Alan-JH/SimUFC/PCBs/Display layers updated/ufc_v4_scratchpad_layer3.step

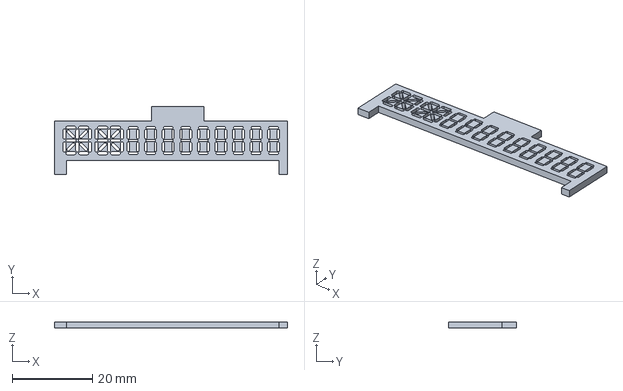
[picture p14: CAD file, 2021-05-30]
PCBs/Display layers updated/ufc_v4_scratchpad_layer3.step
58.0 x 16.8 x 1.60 mm
