Alan-JH/SimUFC/MCAD/STL Export/Key5.stl

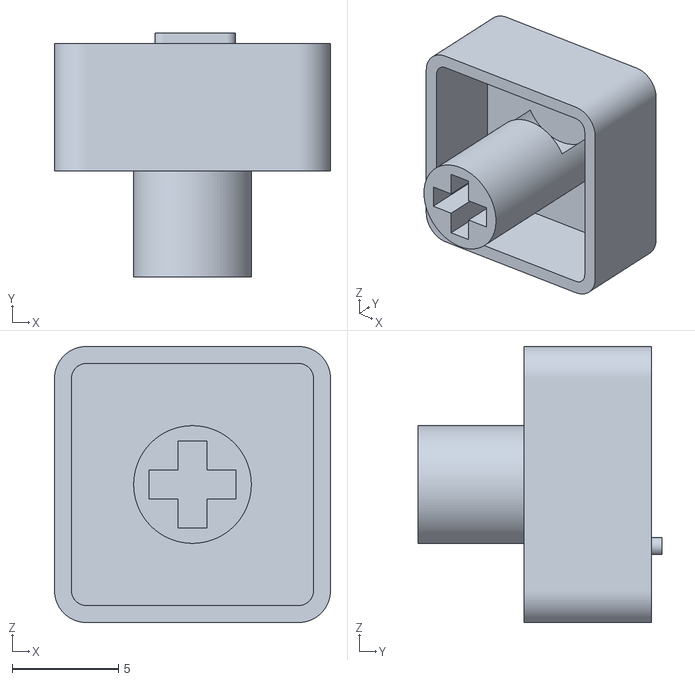
[picture p15: CAD file, 2021-07-18]
MCAD/STL Export/Key5.stl
13.0 x 11.5 x 13.0
