Alan-JH/SimUFC/PCBs/Display layers updated/ufc_v4_opt_layer4.step

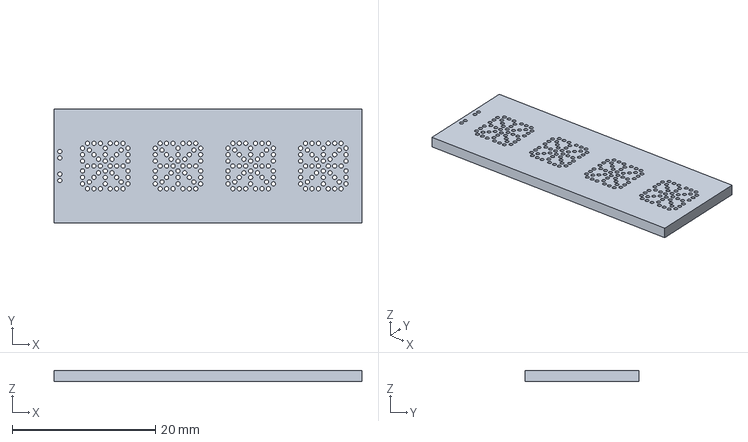
[picture p16: CAD file, 2021-05-30]
PCBs/Display layers updated/ufc_v4_opt_layer4.step
43.1 x 15.9 x 1.60 mm
