Alan-JH/SimUFC/MCAD/STL Export/L side.stl

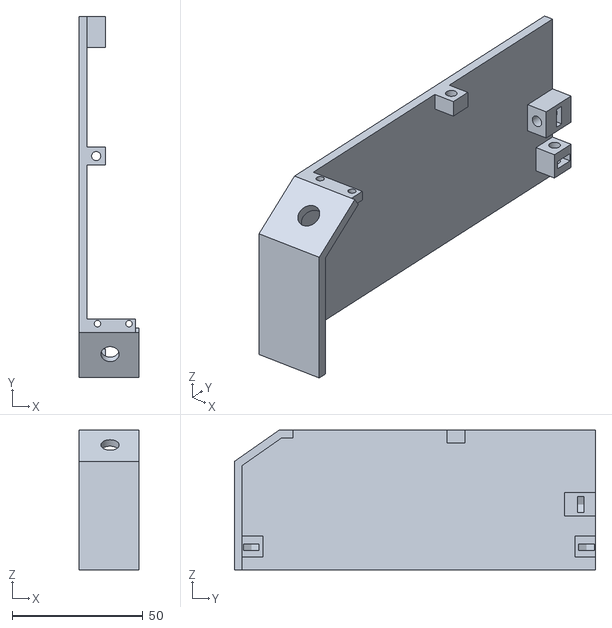
[picture p17: CAD file, 2021-07-18]
MCAD/STL Export/L side.stl
22.8 x 138.3 x 53.6
