Alan-JH/SimUFC/MCAD/STL Export/KeyRound.stl

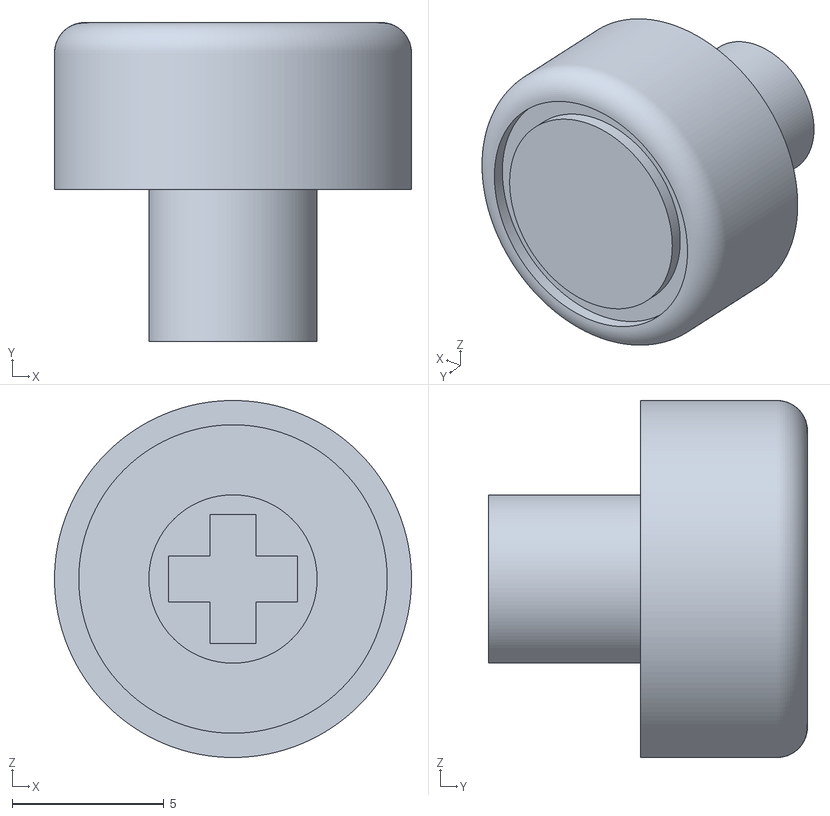
[picture p18: CAD file, 2021-07-18]
MCAD/STL Export/KeyRound.stl
11.8 x 10.5 x 11.8
