Alan-JH/SimUFC/MCAD/STL Export/Face spacer.stl

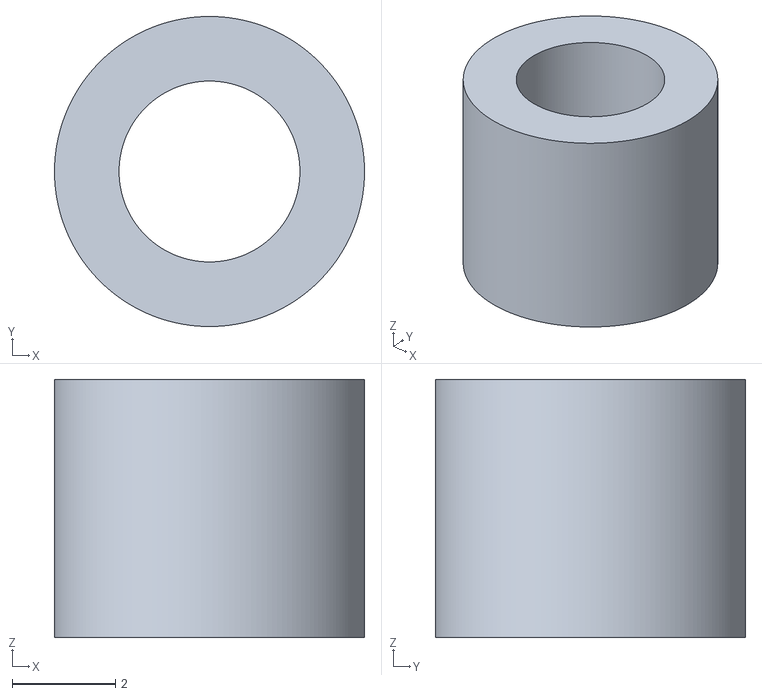
[picture p19: CAD file, 2021-06-10]
MCAD/STL Export/Face spacer.stl
6.00 x 6.00 x 5.00
