Alan-JH/SimUFC/MCAD/STL Export/Top.stl

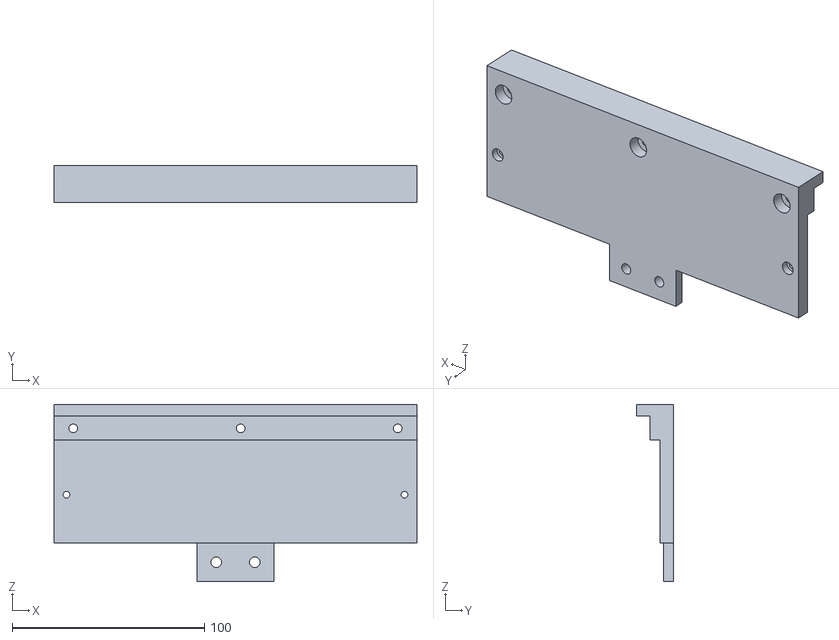
[picture p20: CAD file, 2021-06-10]
MCAD/STL Export/Top.stl
188.6 x 19.0 x 92.0
