Alan-JH/SimUFC/MCAD/STL Export/Face.stl

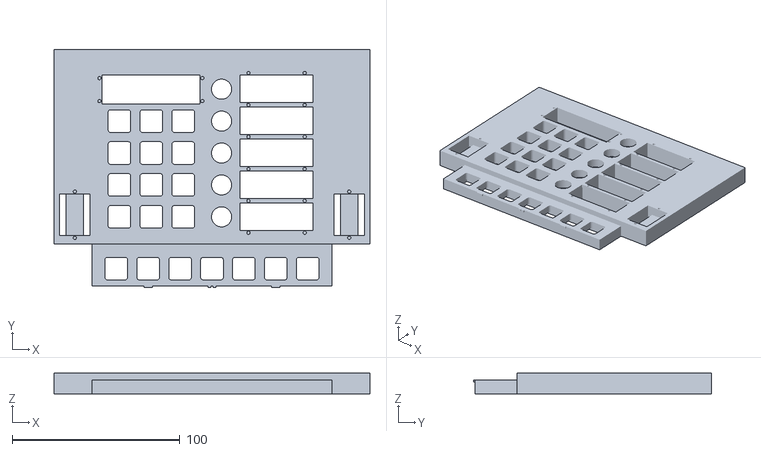
[picture p21: CAD file, 2021-06-10]
MCAD/STL Export/Face.stl
188.6 x 141.9 x 12.4
