Alan-JH/SimUFC/MCAD/STL Export/PCB spacer.stl

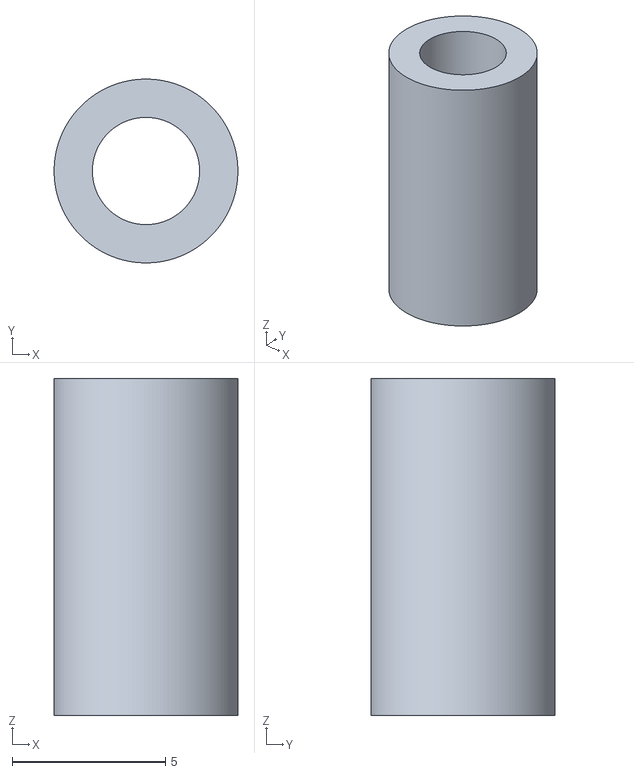
[picture p22: CAD file, 2021-06-08]
MCAD/STL Export/PCB spacer.stl
6.00 x 6.00 x 11.0
