Alan-JH/SimUFC/MCAD/STL Export/COMM retainer.stl

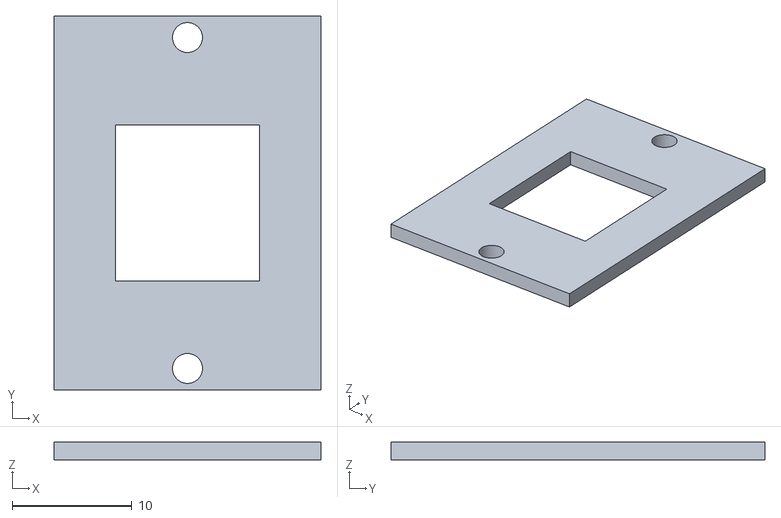
[picture p23: CAD file, 2021-06-08]
MCAD/STL Export/COMM retainer.stl
22.3 x 31.2 x 1.50
