Alan-JH/SimUFC/MCAD/STL Export/Keypadplate.stl

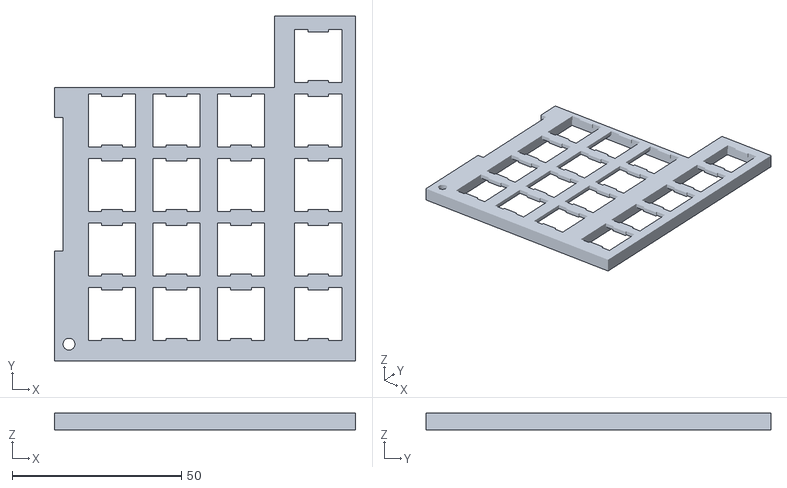
[picture p24: CAD file, 2021-06-08]
MCAD/STL Export/Keypadplate.stl
88.9 x 101.8 x 5.00
