Alan-JH/SimUFC/MCAD/STL Export/Lower bar switch plate.stl

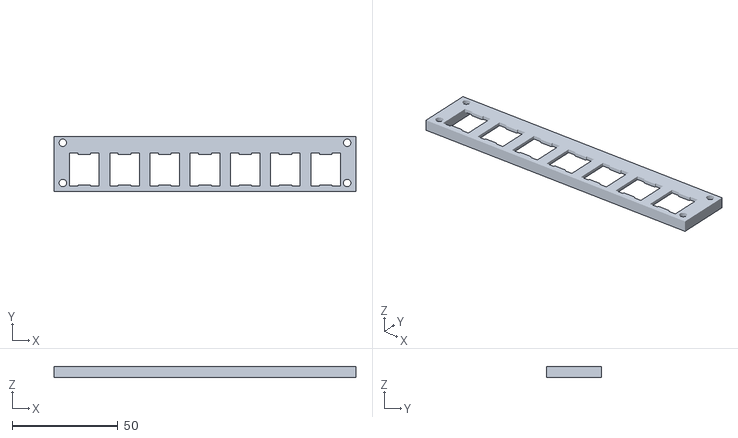
[picture p25: CAD file, 2021-06-08]
MCAD/STL Export/Lower bar switch plate.stl
143.0 x 26.1 x 5.00
