Alan-JH/SimUFC/MCAD/STL Export/Back.stl

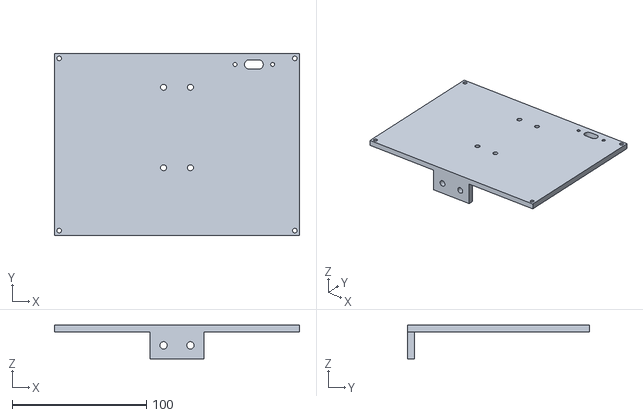
[picture p26: CAD file, 2021-06-08]
MCAD/STL Export/Back.stl
182.6 x 135.3 x 25.0
