Alan-JH/SimUFC/MCAD/STL Export/Scratchpad retainer.stl

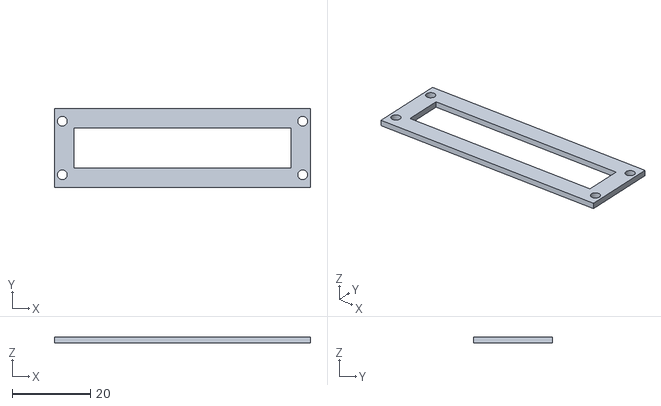
[picture p27: CAD file, 2021-06-08]
MCAD/STL Export/Scratchpad retainer.stl
65.4 x 20.3 x 1.50
