Alan-JH/SimUFC/MCAD/STL Export/OPT retainer.stl

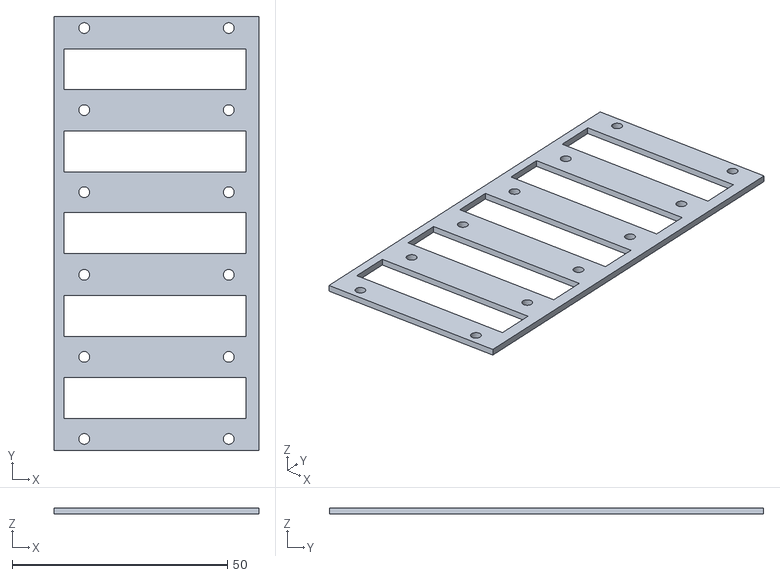
[picture p28: CAD file, 2021-06-08]
MCAD/STL Export/OPT retainer.stl
47.6 x 100.8 x 1.50
