Alan-JH/SimUFC/MCAD/STL Export/Lower bar spacer.stl

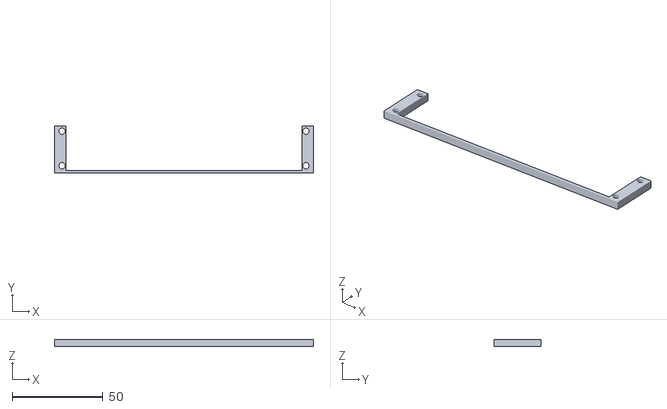
[picture p29: CAD file, 2021-06-08]
MCAD/STL Export/Lower bar spacer.stl
143.0 x 26.1 x 4.00
