Alan-JH/SimUFC/MCAD/STL Export/COMM.stl

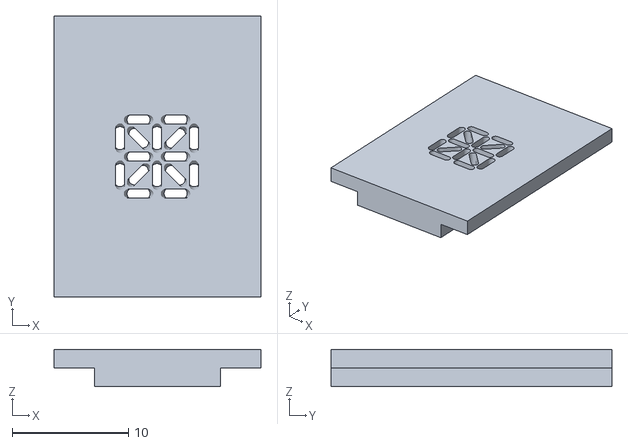
[picture p30: CAD file, 2021-06-08]
MCAD/STL Export/COMM.stl
17.8 x 24.1 x 3.20
