Alan-JH/SimUFC/PCBs/ufc_v4_opt.kicad_pcb

## KiCad design PCBs/ufc_v4_opt.kicad_pcb (2021-05-15)

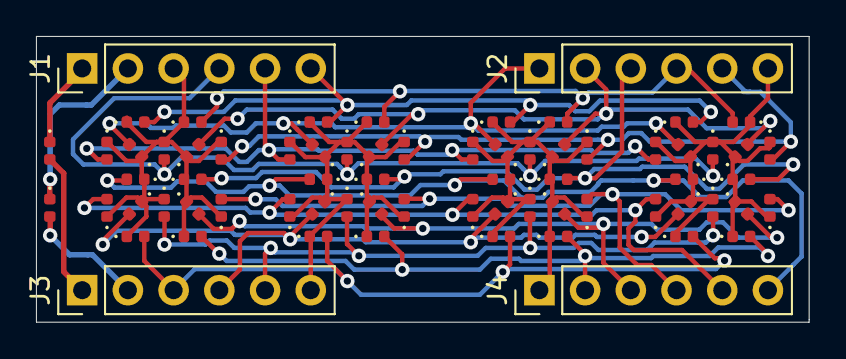
[picture p37: board ufc_v4_opt.kicad_pcb from above]

Board: 2 copper layers, 42.9 x 15.9 mm, 70 parts (0 on the bottom side), 24 nets.

Parts:
D1, D2, D3, D4, D5, D6, D7, D8, D9, D10, D11, D12, D13, D14, D15, D16, D17, D18, D19, D20, D21, D22, D23, D24, D25, D26, D27, D28, D29, D30, D31, D32, D33, D34, D35, D36, D37, D38, D39, D40, D41, D42, D43, D44, D45, D46, D47, D48, D49, D50, D51, D52, D53, D54, D55, D56, D57, D58, D59, D60, D61, D62, D63, D64, D65, D66: LED; LED_0402_1005Metric
J1, J2, J3, J4: Conn_01x06_Male; PinHeader_1x06_P2.54mm_Vertical

Connections:
/DIG0: D1.1, D2.1, D3.1, D4.1, D5.1, D6.1, D7.1, D8.1, D9.1, D10.1, D11.1, D12.1, D13.1, D14.1, D15.1, D16.1, J1.3
/DIG1: D17.1, D18.1, D19.1, D20.1, D21.1, D22.1, D23.1, D24.1, D25.1, D26.1, D27.1, D28.1, D29.1, D30.1, D31.1, D32.1, J3.6
/DIG2: D33.1, D34.1, D35.1, D36.1, D37.1, D38.1, D39.1, D40.1, D41.1, D42.1, D43.1, D44.1, D45.1, D46.1, D47.1, D48.1, J4.1
/DIG3: D49.1, D50.1, D51.1, D52.1, D53.1, D54.1, D55.1, D56.1, D57.1, D58.1, D59.1, D60.1, D61.1, D62.1, D63.1, D64.1, J2.6
/DOT1+: D65.2, J3.1
/DOT1-: D65.1, J1.1
/DOT2+: D66.2, J3.2
/DOT2-: D66.1, J1.2
/SEGA: D7.2, D23.2, D39.2, D55.2, J3.3
/SEGB: D8.2, D24.2, D40.2, D56.2, J1.4
/SEGC: D1.2, D17.2, D33.2, D49.2, J1.5
/SEGD: D3.2, D19.2, D35.2, D51.2, J1.6
/SEGDP: D2.2, D18.2, D34.2, D50.2, J4.5
/SEGE: D6.2, D22.2, D38.2, D54.2, J3.4
/SEGF: D5.2, D21.2, D37.2, D53.2, J4.6
/SEGG: D4.2, D20.2, D36.2, D52.2, J2.1
/SEGH: D9.2, D25.2, D41.2, D57.2, J3.5
/SEGJ: D14.2, D30.2, D46.2, D62.2, J4.2
/SEGK: D13.2, D29.2, D45.2, D61.2, J4.3
/SEGL: D12.2, D28.2, D44.2, D60.2, J2.3
/SEGM: D11.2, D27.2, D43.2, D59.2, J2.2
/SEGN: D10.2, D26.2, D42.2, D58.2, J2.4
/SEGP: D16.2, D32.2, D48.2, D64.2, J4.4
/SEGQ: D15.2, D31.2, D47.2, D63.2, J2.5
