Alan-JH/SimUFC/PCBs/ufc_v4_comm.kicad_pcb

## KiCad design PCBs/ufc_v4_comm.kicad_pcb (2021-05-15)

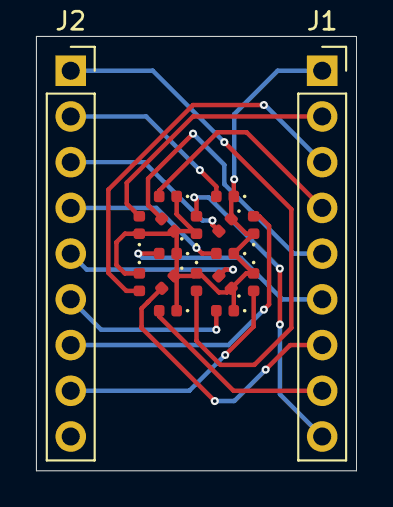
[picture p38: board ufc_v4_comm.kicad_pcb from above]

Board: 2 copper layers, 17.8 x 24.1 mm, 18 parts (0 on the bottom side), 17 nets.

Parts:
D1, D2, D3, D4, D5, D6, D7, D8, D9, D10, D11, D12, D13, D14, D15, D16: LED; LED_0402_1005Metric
J1, J2: Conn_01x09_Male; PinSocket_1x09_P2.54mm_Vertical

Connections:
/COM: D1.1, D2.1, D3.1, D4.1, D5.1, D6.1, D7.1, D8.1, D9.1, D10.1, D11.1, D12.1, D13.1, D14.1, D15.1, D16.1, J1.1
/SEGA: D1.2, J1.2
/SEGB: D2.2, J1.3
/SEGC: D3.2, J1.4
/SEGD: D4.2, J1.5
/SEGDP: D16.2, J2.8
/SEGE: D5.2, J1.6
/SEGF: D6.2, J1.7
/SEGG: D7.2, J1.8
/SEGH: D8.2, J1.9
/SEGJ: D9.2, J2.1
/SEGK: D10.2, J2.2
/SEGL: D11.2, J2.3
/SEGM: D12.2, J2.4
/SEGN: D13.2, J2.5
/SEGP: D14.2, J2.6
/SEGQ: D15.2, J2.7
