Alan-JH/SimUFC/Firmware/UFC_Firmware/CharacterMap.h

//Includes all ascii characters that can be displayed on a 16 segment display, not just those that appear in the hornet UFC, for the sake of future proofing
//Most character patterns are adapted from https://github.com/dmadison/LED-Segment-ASCII
//Two digit numbers also included for those that appear on the COMM displays and Scratchpad digits 1-2

#define lenChars 106
String characters[lenChars] = {
  " ",
  "!",
  "#",
  "$",
  "%",
  "&",
  "'",
  "(",
  ")",
  "*",
  "+",
  ",",
  "-",
  ".",
  "/",
  "0",
  "1",
  "2",
  "3",
  "4",
  "5",
  "6",
  "7",
  "8",
  "9",
  ":",
  ";",
  "<",
  "=",
  ">",
  "?",
  "@",
  "A",
  "B",
  "C",
  "D",
  "E",
  "F",
  "G",
  "H",
  "I",
  "J",
  "K",
  "L",
  "M",
  "N",
  "O",
  "P",
  "Q",
  "R",
  "S",
  "T",
  "U",
  "V",
  "W",
  "X",
  "Y",
  "Z",
  "[",
  "\\",
  "]",
  "^",
  "_",
  "`",
  "a",
  "b",
  "c",
  "d",
  "e",
  "f",
  "g",
  "h",
  "i",
  "j",
  "k",
  "l",
  "m",
  "n",
  "o",
  "p",
  "q",
  "r",
  "s",
  "t",
  "u",
  "v",
  "w",
  "x",
  "y",
  "z",
  "{",
  "|",
  "}",
  "~",
  "10", //Specifically for the Hornet UFC's Scratchpad + COMM:
  "11",
  "12",
  "13",
  "14",
  "15",
  "16",
  "17",
  "18",
  "19",
  "20", 
  //Specifically because DCS BIOS is weird:
  "--"
};

/* 7 Seg: A, B, C, D, E, F, G
   index: 0, 1, 2, 3, 4, 5, 6
   --A--
  |     |
  |     |
  F     B
  |     |
  |     |
   --G--
  |     |
  |     |
  E     C
  |     |
  |     |
   --D--

 */

 uint8_t Map7[94][7] = {
  {0, 0, 0, 0, 0, 0, 0},
  {0, 1, 1, 0, 0, 0, 0},
  {0, 1, 1, 1, 1, 1, 1},
  {1, 0, 1, 1, 0, 1, 1},
  {0, 1, 0, 0, 1, 0, 1},
  {0, 1, 1, 0, 0, 0, 1},
  {0, 0, 0, 0, 0, 1, 0},
  {1, 0, 0, 1, 0, 1, 0},
  {1, 1, 0, 1, 0, 0, 0},
  {1, 0, 0, 0, 0, 1, 0},
  {0, 0, 0, 0, 1, 1, 1},
  {0, 0, 0, 0, 1, 0, 0},
  {0, 0, 0, 0, 0, 0, 1},
  {0, 0, 1, 1, 1, 0, 1},
  {0, 1, 0, 0, 1, 0, 1},
  {1, 1, 1, 1, 1, 1, 0},
  {0, 1, 1, 0, 0, 0, 0},
  {1, 1, 0, 1, 1, 0, 1},
  {1, 1, 1, 1, 0, 0, 1},
  {0, 1, 1, 0, 0, 1, 1},
  {1, 0, 1, 1, 0, 1, 1},
  {0, 0, 1, 1, 1, 1, 1},
  {1, 1, 1, 0, 0, 0, 0},
  {1, 1, 1, 1, 1, 1, 1},
  {1, 1, 1, 0, 0, 1, 1},
  {1, 0, 0, 1, 0, 0, 0},
  {1, 0, 1, 1, 0, 0, 0},
  {1, 0, 0, 0, 0, 1, 1},
  {0, 0, 0, 1, 0, 0, 1},
  {1, 1, 0, 0, 0, 0, 1},
  {1, 1, 0, 0, 1, 0, 1},
  {1, 1, 0, 0, 0, 1, 1},
  {1, 1, 1, 0, 1, 1, 1},
  {0, 0, 1, 1, 1, 1, 1},
  {1, 0, 0, 1, 1, 1, 0},
  {0, 1, 1, 1, 1, 0, 1},
  {1, 0, 0, 1, 1, 1, 1},
  {1, 0, 0, 0, 1, 1, 1},
  {1, 0, 1, 1, 1, 1, 0},
  {0, 1, 1, 0, 1, 1, 1},
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
 };

/*16 Seg: A, B, C, D, E, F, G, H, I, J, K, L, M, N, O, P
 *index:  0, 1, 2, 3, 4, 5, 6, 7, 8, 9,10,11,12,13,14,15
   --A-- --B--
  |\    |    /|
  | \   |   / |
  H  I  J  K  C
  |   \ | /   |
  |    \|/    |
   --P-- --L--
  |    /|\    |
  |   / | \   |
  G  O  N  M  D
  | /   |   \ |
  |/    |    \|
   --F-- --E--
*/
uint8_t Map16[106][16] = {
 //A, B, C, D, E, F, G, H, I, J, K, L, M, N, O, P
  {0, 0, 0, 0, 0, 0, 0, 0, 0, 0, 0, 0, 0, 0, 0, 0},
  {0, 0, 1, 1, 0, 0, 0, 0, 0, 0, 0, 0, 0, 0, 0, 0},
  {0, 0, 1, 1, 1, 1, 0, 0, 0, 1, 0, 1, 0, 1, 0, 1},
  {1, 1, 0, 1, 1, 1, 0, 1, 0, 1, 0, 1, 0, 1, 0, 1},
  {1, 0, 0, 1, 1, 0, 0, 1, 0, 1, 1, 1, 0, 1, 1, 1},
  {1, 0, 0, 0, 1, 1, 1, 0, 1, 1, 0, 0, 1, 0, 0, 1},
  {0, 0, 0, 0, 0, 0, 0, 0, 0, 1, 0, 0, 0, 0, 0, 0},
  {0, 0, 0, 0, 0, 0, 0, 0, 0, 0, 1, 0, 1, 0, 0, 0},
  {0, 0, 0, 0, 0, 0, 0, 0, 1, 0, 0, 0, 0, 0, 1, 0},
  {0, 0, 0, 0, 0, 0, 0, 0, 1, 1, 1, 1, 1, 1, 1, 1},
  {0, 0, 0, 0, 0, 0, 0, 0, 0, 1, 0, 1, 0, 1, 0, 1},
  {0, 0, 0, 0, 0, 0, 0, 0, 0, 0, 0, 0, 0, 0, 1, 0},
  {0, 0, 0, 0, 0, 0, 0, 0, 0, 0, 0, 1, 0, 0, 0, 1},
  {0, 0, 0, 1, 1, 0, 0, 0, 0, 0, 0, 1, 0, 1, 0, 0},
  {0, 0, 0, 0, 0, 0, 0, 0, 0, 0, 1, 0, 0, 0, 1, 0},
  {0, 1, 1, 1, 1, 0, 0, 0, 0, 1, 0, 0, 0, 1, 0, 0}, //0
  {0, 0, 1, 1, 0, 0, 0, 0, 0, 0, 0, 0, 0, 0, 0, 0}, //1
  {0, 1, 1, 0, 1, 0, 0, 0, 0, 0, 0, 1, 0, 1, 0, 0}, //2
  {0, 1, 1, 1, 1, 0, 0, 0, 0, 0, 0, 1, 0, 0, 0, 0}, //3
  {0, 0, 1, 1, 0, 0, 0, 0, 0, 1, 0, 1, 0, 0, 0, 0}, //4
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
  {0, 1, 1, 1, 0, 0, 1, 1, 0, 0, 0, 0, 0, 0, 0, 0},
  {0, 1, 1, 1, 1, 0, 1, 1, 0, 1, 0, 1, 0, 1, 0, 0},
  {0, 1, 1, 1, 0, 0, 1, 1, 0, 1, 0, 1, 0, 0, 0, 0},
  {1, 1, 1, 1, 1, 1, 1, 0, 0, 1, 0, 0, 0, 1, 0, 1},
  {0, 0, 0, 0, 0, 0, 0, 0, 0, 0, 0, 1, 0, 0, 0, 1} //--
};
