Alan-JH/SimUFC/Firmware/UFC_Firmware/SegmentMap.h

/*16 Seg: A, B, C, D, E, F, G, H, I, J, K, L, M, N, O, P
 *index:  0, 1, 2, 3, 4, 5, 6, 7, 8, 9,10,11,12,13,14,15
   --A-- --B--
  |\    |    /|
  | \   |   / |
  H  I  J  K  C
  |   \ | /   |
  |    \|/    |
   --P-- --L--
  |    /|\    |
  |   / | \   |
  G  O  N  M  D
  | /   |   \ |
  |/    |    \|
   --F-- --E--

7 Seg: A, B, C, D, E, F, G
index: 0, 1, 2, 3, 4, 5, 6
   --A--
  |     |
  |     |
  F     B
  |     |
  |     |
   --G--
  |     |
  |     |
  E     C
  |     |
  |     |
   --D--

*/

//Scratchpad digits 1 and 2
uint8_t ScratchPad16[2][16][2] = {
  {{8, 6}, {9, 7}, {9, 2}, {9,1}, {9, 3}, {8, 2}, {8, 7}, {16, 0}, {8, 5}, {8, 1}, {9, 6}, {9, 5}, {9, 4}, {17, 0}, {8, 3}, {8, 4}},
  {{10, 6}, {11, 7}, {11, 2}, {11, 1}, {11, 3}, {10, 2}, {10, 7}, {18, 0}, {10, 5}, {10, 1}, {11, 6}, {11, 5}, {11, 4}, {19, 0}, {10, 3}, {10, 4}}
};

//Scratchpad digits 3-11
uint8_t ScratchPad7[9][7][2] = {
  {{20, 0}, {12, 7}, {12, 6}, {12, 5}, {12, 4}, {12, 3}, {12, 2}},
  {{21, 0}, {13, 7}, {13, 6}, {13, 5}, {13, 4}, {13, 3}, {13, 2}},
  {{22, 0}, {14, 7}, {14, 6}, {14, 5}, {14, 4}, {14, 3}, {14, 2}},
  {{23, 0}, {15, 7}, {15, 6}, {15, 5}, {15, 4}, {15, 3}, {15, 2}},
  {{12, 1}, {12, 0}, {4, 7}, {4, 6}, {4, 5}, {4, 4}, {4, 3}},
  {{13, 1}, {13, 0}, {5, 7}, {5, 6}, {5, 5}, {5, 4}, {5, 3}},
  {{14, 1}, {14, 0}, {6, 7}, {6, 6}, {6, 5}, {6, 4}, {6, 3}},
  {{15, 1}, {15, 0}, {7, 7}, {7, 6}, {7, 5}, {7, 4}, {7, 3}},
  {{8, 9}, {8, 8}, {0, 15}, {0, 14}, {0, 13}, {0, 12}, {0, 11}}
};

//OPT1 DOT
uint8_t OPT1Dot[1][1][2] = {
  {{1, 8}}
};

//OPT1 digits 1-4
uint8_t OPT1Disp[4][16][2] = {
  {{9, 13}, {1, 12}, {1, 10}, {1, 11}, {9, 8}, {17, 8}, {1, 9}, {9, 14}, {9, 10}, {9, 15}, {1, 13}, {1, 14}, {1, 15}, {9, 9}, {9, 12}, {9, 11}},
  {{10, 13}, {2, 12}, {2, 10}, {2, 11}, {10, 8}, {18, 8}, {2, 9}, {10, 14}, {10, 10}, {10, 15}, {2, 13}, {2, 14}, {2, 15}, {10, 9}, {10, 12}, {10, 11}},
  {{11, 13}, {3, 12}, {3, 10}, {3, 11}, {11, 8}, {19, 8}, {3, 9}, {11, 14}, {11, 10}, {11, 15}, {3, 13}, {3, 14}, {3, 15}, {11, 9}, {11, 12}, {11, 11}},
  {{12, 13}, {4, 12}, {4, 10}, {4, 11}, {12, 8}, {20, 8}, {4, 9}, {12, 14}, {12, 10}, {12, 15}, {4, 13}, {4, 14}, {4, 15}, {12, 9}, {12, 12}, {12, 11}}
};

//OPT2 DOT
uint8_t OPT2Dot[1][1][2] = {
  {{40, 0}}
};

//OPT2 digits 1-4
uint8_t OPT2Disp[4][16][2] = {
  {{24, 3}, {32, 4}, {32, 6}, {32, 5}, {32, 0}, {24, 0}, {32, 7}, {24, 2}, {24, 6}, {24, 1}, {32, 3}, {32, 2}, {32, 1}, {24, 7}, {24, 4}, {24, 5}},
  {{25, 3}, {33, 4}, {33, 6}, {33, 5}, {33, 0}, {25, 0}, {33, 7}, {25, 2}, {25, 6}, {25, 1}, {33, 3}, {33, 2}, {33, 1}, {25, 7}, {25, 4}, {25, 5}},
  {{26, 3}, {34, 4}, {34, 6}, {34, 5}, {34, 0}, {26, 0}, {34, 7}, {26, 2}, {26, 6}, {26, 1}, {34, 3}, {34, 2}, {34, 1}, {26, 7}, {26, 4}, {26, 5}},
  {{27, 3}, {35, 4}, {35, 6}, {35, 5}, {35, 0}, {27, 0}, {35, 7}, {27, 2}, {27, 6}, {27, 1}, {35, 3}, {35, 2}, {35, 1}, {27, 7}, {27, 4}, {27, 5}}
};

//OPT3 DOT
uint8_t OPT3Dot[1][1][2] = {
  {{44, 0}}
};

//OPT3 digits 1-4
uint8_t OPT3Disp[4][16][2] = {
  {{28, 3}, {36, 4}, {36, 6}, {36, 5}, {36, 0}, {28, 0}, {36, 7}, {28, 2}, {28, 6}, {28, 1}, {36, 3}, {36, 2}, {36, 1}, {28, 7}, {28, 4}, {28, 5}},
  {{29, 3}, {37, 4}, {37, 6}, {37, 5}, {37, 0}, {29, 0}, {37, 7}, {29, 2}, {29, 6}, {29, 1}, {37, 3}, {37, 2}, {37, 1}, {29, 7}, {29, 4}, {29, 5}},
  {{30, 3}, {38, 4}, {38, 6}, {38, 5}, {38, 0}, {30, 0}, {38, 7}, {30, 2}, {30, 6}, {30, 1}, {38, 3}, {38, 2}, {38, 1}, {30, 7}, {30, 4}, {30, 5}},
  {{31, 3}, {39, 4}, {39, 6}, {39, 5}, {39, 0}, {31, 0}, {39, 7}, {31, 2}, {31, 6}, {31, 1}, {39, 3}, {39, 2}, {39, 1}, {31, 7}, {31, 4}, {31, 5}}
};

//OPT 4 DOT
uint8_t OPT4Dot[1][1][2] = {
  {{40, 8}}
};

//OPT 4 digits 1-4
uint8_t OPT4Disp[4][16][2] = {
  {{24, 11}, {32, 12}, {32, 14}, {32, 13}, {32, 8}, {24, 8}, {32, 15}, {24, 10}, {24, 14}, {24, 9}, {32, 11}, {32, 10}, {32, 9}, {24, 15}, {24, 12}, {24, 13}},
  {{25, 11}, {33, 12}, {33, 14}, {33, 13}, {33, 8}, {25, 8}, {33, 15}, {25, 10}, {25, 14}, {25, 9}, {33, 11}, {33, 10}, {33, 9}, {25, 15}, {25, 12}, {25, 13}},
  {{26, 11}, {34, 12}, {34, 14}, {34, 13}, {34, 8}, {26, 8}, {34, 15}, {26, 10}, {26, 14}, {26, 9}, {34, 11}, {34, 10}, {34, 9}, {26, 15}, {26, 12}, {26, 13}},
  {{27, 11}, {35, 12}, {35, 14}, {35, 13}, {35, 8}, {27, 8}, {35, 15}, {27, 10}, {27, 14}, {27, 9}, {35, 11}, {35, 10}, {35, 9}, {27, 15}, {27, 12}, {27, 13}}
};

//OPT 5 DOT
uint8_t OPT5Dot[1][1][2] = {
  {{44, 8}}
};

//OPT 5 digits 1-4
uint8_t OPT5Disp[4][16][2] = {
  {{28, 11}, {36, 12}, {36, 14}, {36, 13}, {36, 8}, {28, 8}, {36, 15}, {28, 10}, {28, 14}, {28, 9}, {36, 11}, {36, 10}, {36, 9}, {28, 15}, {28, 12}, {28, 13}},
  {{29, 11}, {37, 12}, {37, 14}, {37, 13}, {37, 8}, {29, 8}, {37, 15}, {29, 10}, {29, 14}, {29, 9}, {37, 11}, {37, 10}, {37, 9}, {29, 15}, {29, 12}, {29, 13}},
  {{30, 11}, {38, 12}, {38, 14}, {38, 13}, {38, 8}, {30, 8}, {38, 15}, {30, 10}, {30, 14}, {30, 9}, {38, 11}, {38, 10}, {38, 9}, {30, 15}, {30, 12}, {30, 13}},
  {{31, 11}, {39, 12}, {39, 14}, {39, 13}, {39, 8}, {31, 8}, {39, 15}, {31, 10}, {31, 14}, {31, 9}, {39, 11}, {39, 10}, {39, 9}, {31, 15}, {31, 12}, {31, 13}}
};

//COMM 1
uint8_t COMM1[1][16][2] = {
  {{6, 11}, {14, 12}, {14, 15}, {22, 8}, {14, 14}, {6, 15}, {6, 10}, {6, 9}, {6, 12}, {14, 8}, {14, 11}, {14, 10}, {14, 13}, {14, 9}, {6, 14}, {6, 13}}
};

//COMM 2
uint8_t COMM2[1][16][2] = {
  {{5, 11}, {13, 12}, {13, 15}, {21, 8}, {13, 14}, {5, 15}, {5, 10}, {5, 9}, {5, 12}, {13, 8}, {13, 11}, {13, 10}, {13, 13}, {13, 9}, {5, 14}, {5, 13}}
};
